Darkops-cpu/GameBoy/New Board/Hades/Battery.kicad_sch

## KiCad design New Board/Hades/Battery.kicad_sch (2026-08-04)

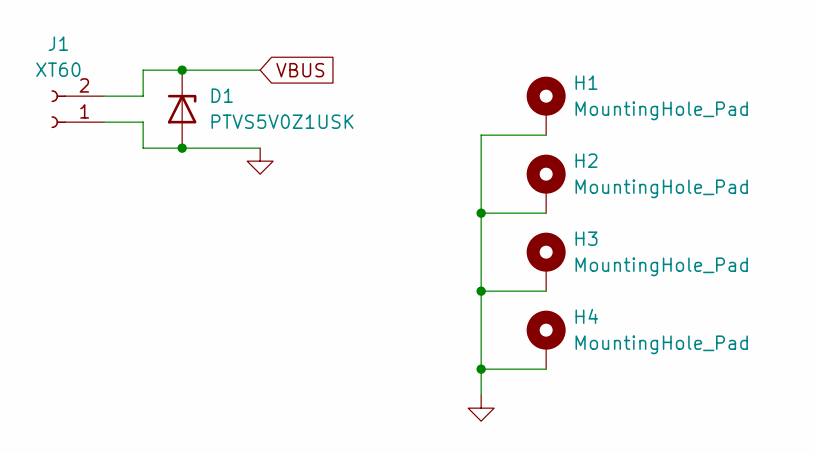
[picture p9: schematic Battery.kicad_sch]

Parts:
D1: PTVS5V0Z1USK; Nexperia_DSN1608-2_1.6x0.8mm
H1, H2, H3, H4: MountingHole_Pad; MountingHole_3.2mm_M3_Pad_Via
J1: XT60; AMASS_XT60-M_1x02_P7.20mm_Vertical

Connections:
GND: D1.2 (A), H1.1, H2.1, H3.1, H4.1, J1.1
VBUS: D1.1 (K), J1.2
