Darkops-cpu/GameBoy/New Board/Hades/ESP32.kicad_sch

## KiCad design New Board/Hades/ESP32.kicad_sch (2026-08-04)

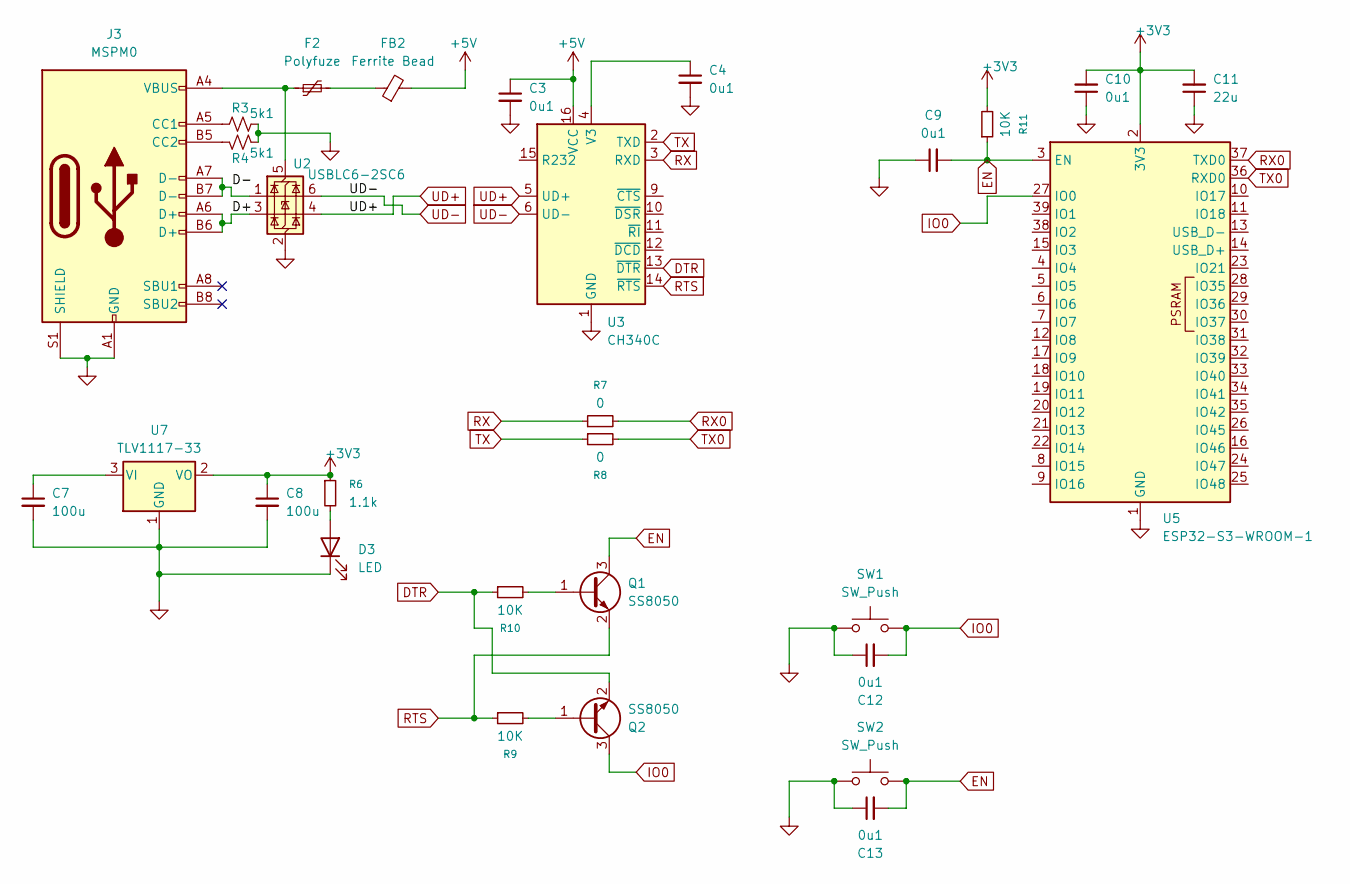
[picture p10: schematic ESP32.kicad_sch]

Parts:
C3, C4, C9, C10, C12, C13: 0u1
C7, C8: 100u
C11: 22u
D3: LED
F2: Polyfuze
FB2: Ferrite Bead
J3: MSPM0; USB_C_Receptacle_GCT_USB4105-xx-A_16P_TopMnt_Horizontal
Q1, Q2: SS8050; SOT-23
R3, R4: 5k1; R_0603_1608Metric_Pad0.98x0.95mm_HandSolder
R6: 1.1k
R7, R8: 0
R9, R10, R11: 10K
SW1, SW2: SW_Push; SW_Push_1P1T_NO_CK_KMR2
U2: USBLC6-2SC6; SOT-23-6
U3: CH340C; SOIC-16_3.9x9.9mm_P1.27mm
U5: ESP32-S3-WROOM-1
U7: TLV1117-33; SOT-223-3_TabPin2

Connections:
+3V3: C8.1, C10.2, C11.2, R6.1, R11.2, U5.2 (3V3), U7.2 (VO)
+5V: C3.1, FB2.2, U3.16 (VCC)
D+: J3.A6 (D+), J3.B6 (D+), U2.3 (I/O2)
D-: J3.A7 (D-), J3.B7 (D-), U2.1 (I/O1)
DTR: Q2.2 (E), R10.1, U3.13 (~DTR)
EN: C9.2, C13.2, Q1.3 (C), R11.1, SW2.2, U5.3 (EN)
GND: C3.2, C4.2, C7.2, C8.2, C9.1, C10.1, C11.1, C12.1, C13.1, D3.1 (K), J3.A1 (GND), J3.A12 (GND), J3.B1 (GND), J3.B12 (GND), J3.S1 (SHIELD), R3.2, R4.2, SW1.1, SW2.1, U2.2 (GND), U3.1 (GND), U5.1 (GND), U5.40 (GND), U5.41 (GND), U7.1 (GND)
IO0: C12.2, Q2.3 (C), SW1.2, U5.27 (IO0)
unnamed: C4.1, U3.4 (V3)
unnamed: C7.1, U7.3 (VI)
unnamed: D3.2 (A), R6.2
unnamed: F2.1, J3.A4 (VBUS), J3.A9 (VBUS), J3.B4 (VBUS), J3.B9 (VBUS), U2.5 (VBUS)
unnamed: F2.2, FB2.1
unnamed: J3.A5 (CC1), R3.1
unnamed: J3.B5 (CC2), R4.1
unnamed: Q1.1 (B), R10.2
unnamed: Q2.1 (B), R9.2
RTS: Q1.2 (E), R9.1, U3.14 (~RTS)
RX: R7.1, U3.3 (RXD)
RX0: R7.2, U5.37 (TXD0)
TX: R8.1, U3.2 (TXD)
TX0: R8.2, U5.36 (RXD0)
UD+: U2.4 (I/O2), U3.5 (UD+)
UD-: U2.6 (I/O1), U3.6 (UD-)
