Darkops-cpu/GameBoy/New Board/Hades/MSPM0.kicad_sch

## KiCad design New Board/Hades/MSPM0.kicad_sch (2026-08-04)

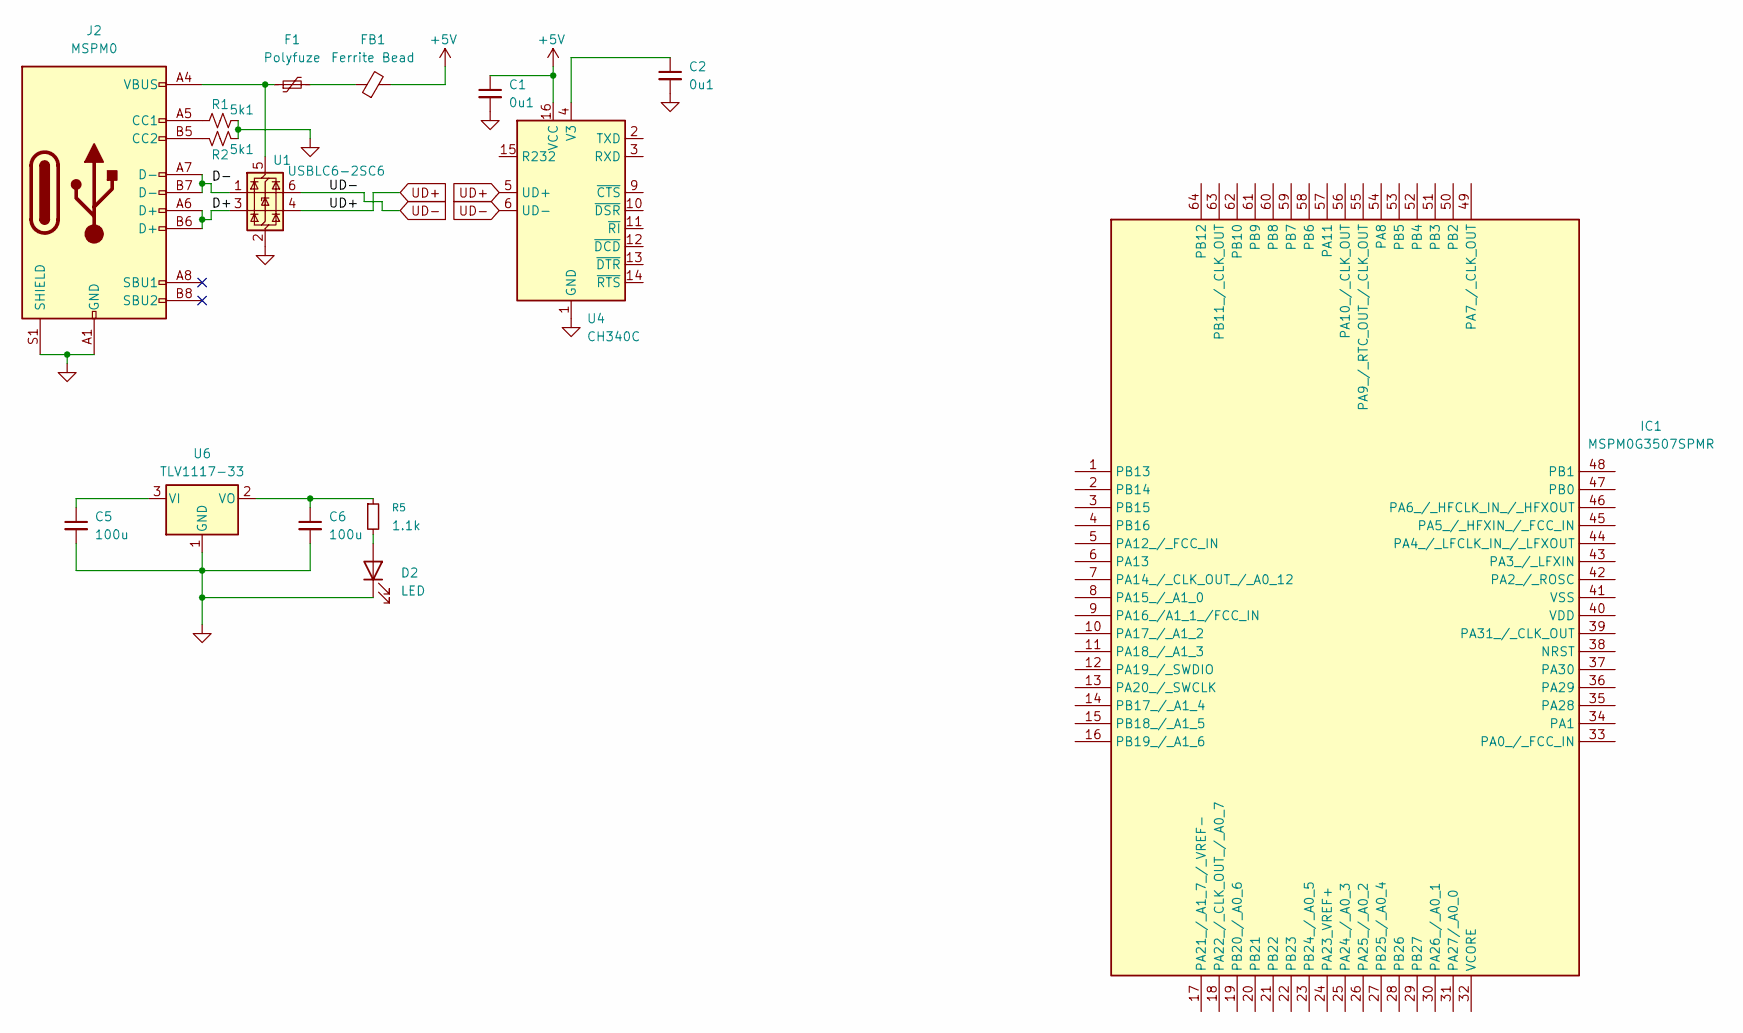
[picture p11: schematic MSPM0.kicad_sch]

Parts:
C1, C2: 0u1
C5, C6: 100u
D2: LED
F1: Polyfuze
FB1: Ferrite Bead
IC1: MSPM0G3507SPMR; QFP50P1200X1200X160-64N; Mouser Part Number 595-MSPM0G3507SPMR
J2: MSPM0; USB_C_Receptacle_GCT_USB4105-xx-A_16P_TopMnt_Horizontal
R1, R2: 5k1; R_0603_1608Metric_Pad0.98x0.95mm_HandSolder
R5: 1.1k
U1: USBLC6-2SC6; SOT-23-6
U4: CH340C; SOIC-16_3.9x9.9mm_P1.27mm
U6: TLV1117-33; SOT-223-3_TabPin2

Connections:
+5V: C1.1, FB1.2, U4.16 (VCC)
D+: J2.A6 (D+), J2.B6 (D+), U1.3 (I/O2)
D-: J2.A7 (D-), J2.B7 (D-), U1.1 (I/O1)
GND: C1.2, C2.2, C5.2, C6.2, D2.1 (K), J2.A1 (GND), J2.A12 (GND), J2.B1 (GND), J2.B12 (GND), J2.S1 (SHIELD), R1.2, R2.2, U1.2 (GND), U4.1 (GND), U6.1 (GND)
unnamed: C2.1, U4.4 (V3)
unnamed: C5.1, U6.3 (VI)
unnamed: C6.1, R5.1, U6.2 (VO)
unnamed: D2.2 (A), R5.2
unnamed: F1.1, J2.A4 (VBUS), J2.A9 (VBUS), J2.B4 (VBUS), J2.B9 (VBUS), U1.5 (VBUS)
unnamed: F1.2, FB1.1
unnamed: J2.A5 (CC1), R1.1
unnamed: J2.B5 (CC2), R2.1
UD+: U1.4 (I/O2), U4.5 (UD+)
UD-: U1.6 (I/O1), U4.6 (UD-)
